todi-mih/TSC-project/Images/Screenshot 2025-04-05 224327.png

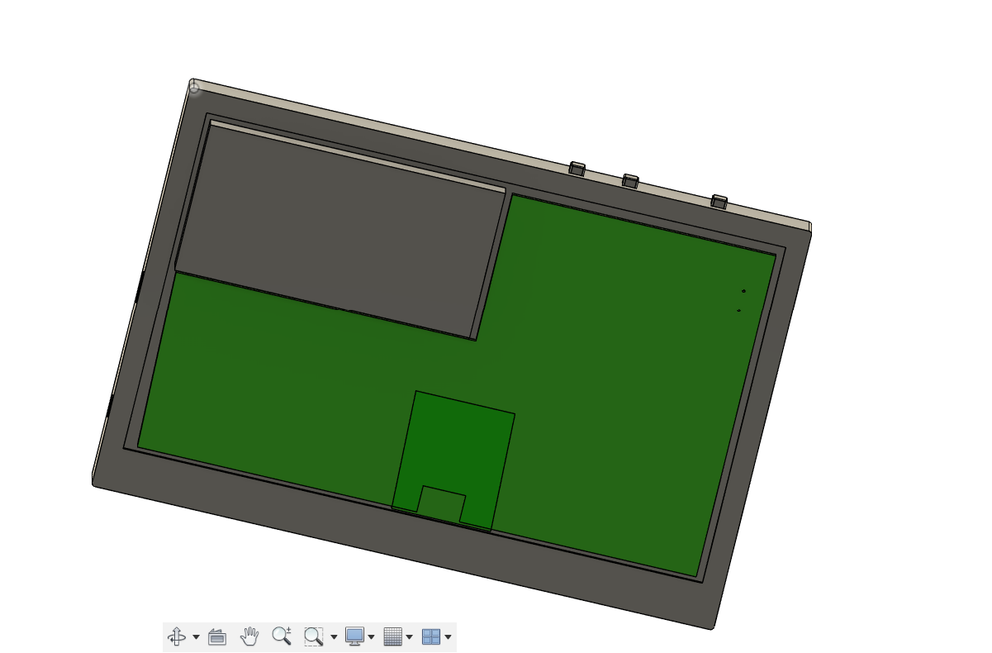
Images/Screenshot 2025-04-05 224327.png
